dschil138/Fulcrum/STLs/thumb-keycap-vertical.stl

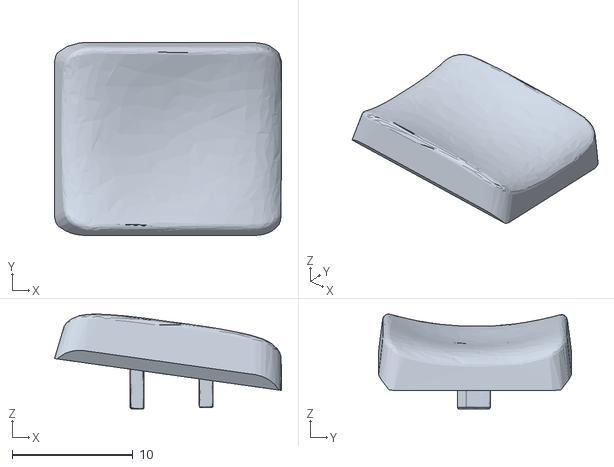
[picture p24: CAD file, 2023-01-18]
STLs/thumb-keycap-vertical.stl
18.8 x 16.0 x 7.86
