dschil138/Fulcrum/STLs/key-riser-slant.stl

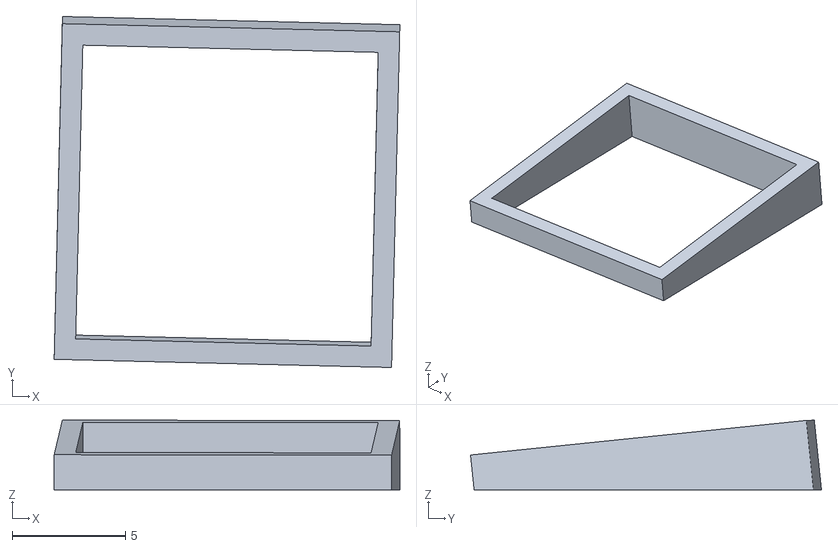
[picture p25: CAD file, 2023-01-13]
STLs/key-riser-slant.stl
15.3 x 15.5 x 3.08
