dschil138/Fulcrum/STLs/joystick.stl

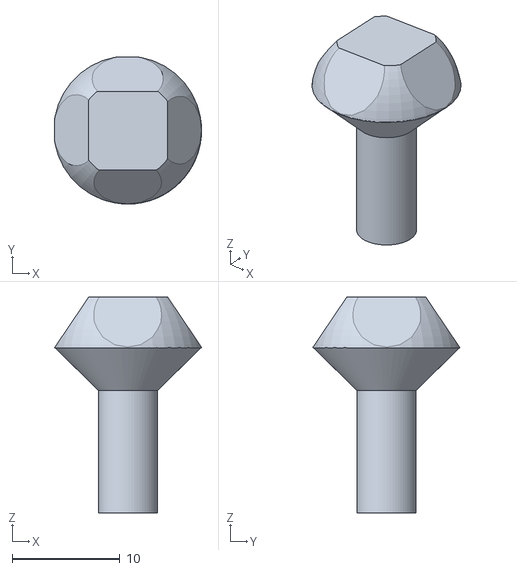
[picture p26: CAD file, 2023-01-13]
STLs/joystick.stl
13.6 x 13.6 x 20.0
