dschil138/Fulcrum/STLs/key-riser.stl

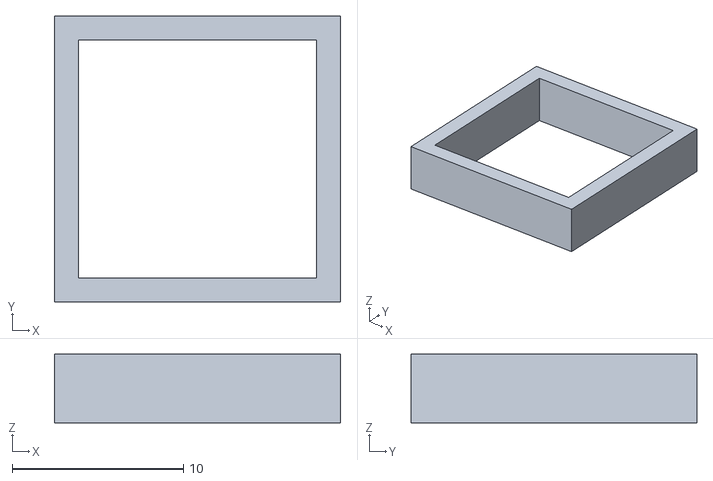
[picture p27: CAD file, 2023-01-13]
STLs/key-riser.stl
16.7 x 16.7 x 4.00
