dschil138/Fulcrum/STLs/rotary-cap.stl

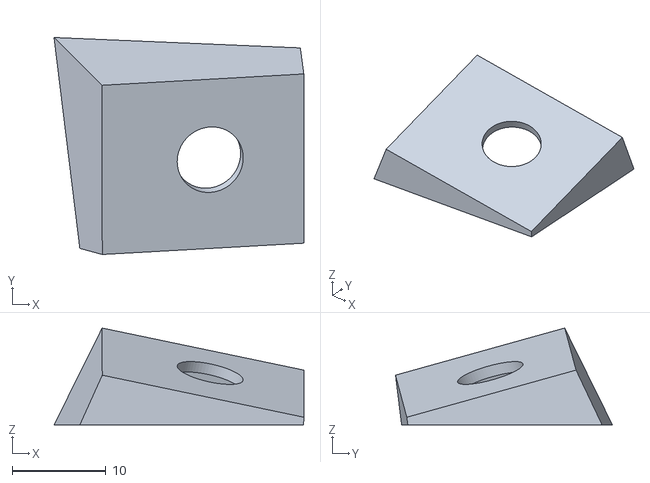
[picture p28: CAD file, 2023-01-13]
STLs/rotary-cap.stl
26.7 x 23.2 x 10.3
