dschil138/Fulcrum/src/20-key/kb.py

import board
from kmk.kmk_keyboard import KMKKeyboard as _KMKKeyboard
from kmk.scanners import DiodeOrientation

class KMKKeyboard(_KMKKeyboard):
    col_pins = (board.D11, board.D10, board.D9, board.D7, board.SCL, board.SDA, board.TX, board.RX)
    row_pins = (board.A0, board.A1, board.A2, board.A3)
    diode_orientation = DiodeOrientation.COL2ROW
